antevens/smart-wallplate/docs/renders/eu_5v_board_copper_back.png

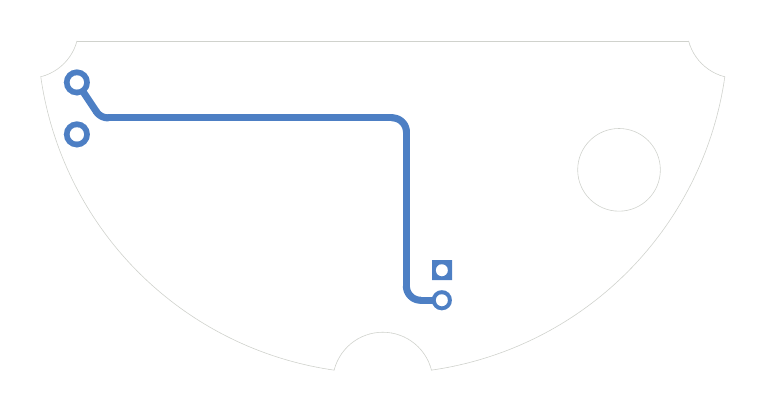
docs/renders/eu_5v_board_copper_back.png
