antevens/smart-wallplate/docs/renders/eu_back.png

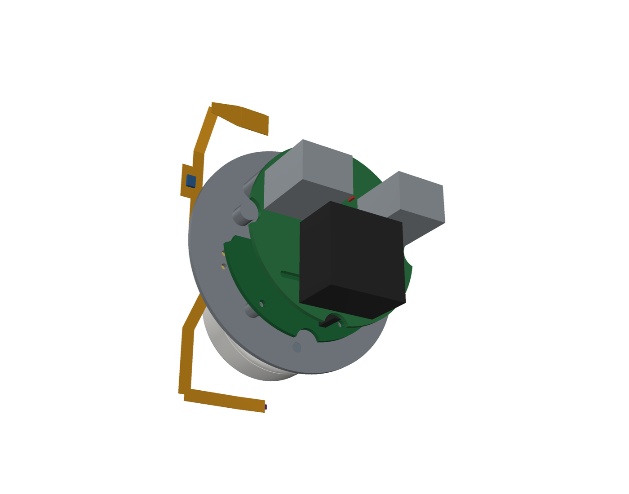
docs/renders/eu_back.png
