antevens/smart-wallplate/docs/renders/power_jumper_copper_back.png

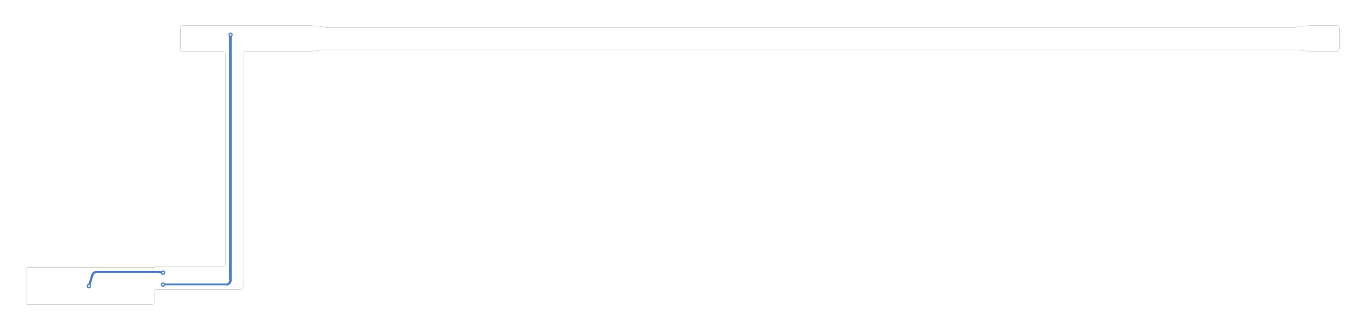
docs/renders/power_jumper_copper_back.png
