antevens/smart-wallplate/reference/v0.1-openscad/renders/01_front.png

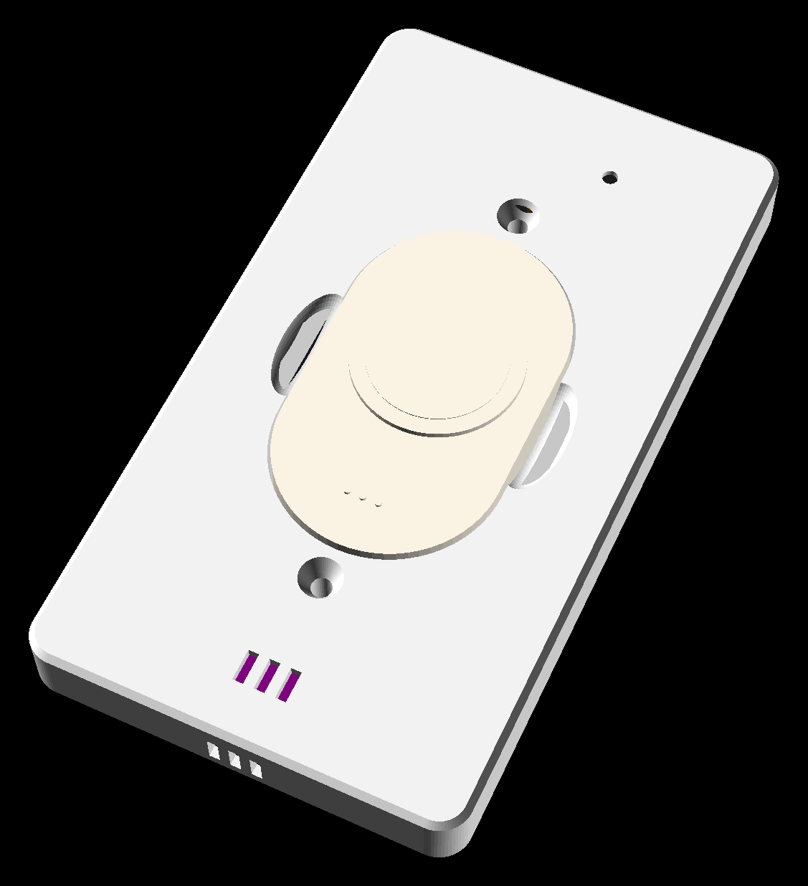
reference/v0.1-openscad/renders/01_front.png
