antevens/smart-wallplate/reference/v0.1-openscad/renders/02_remote_out.png

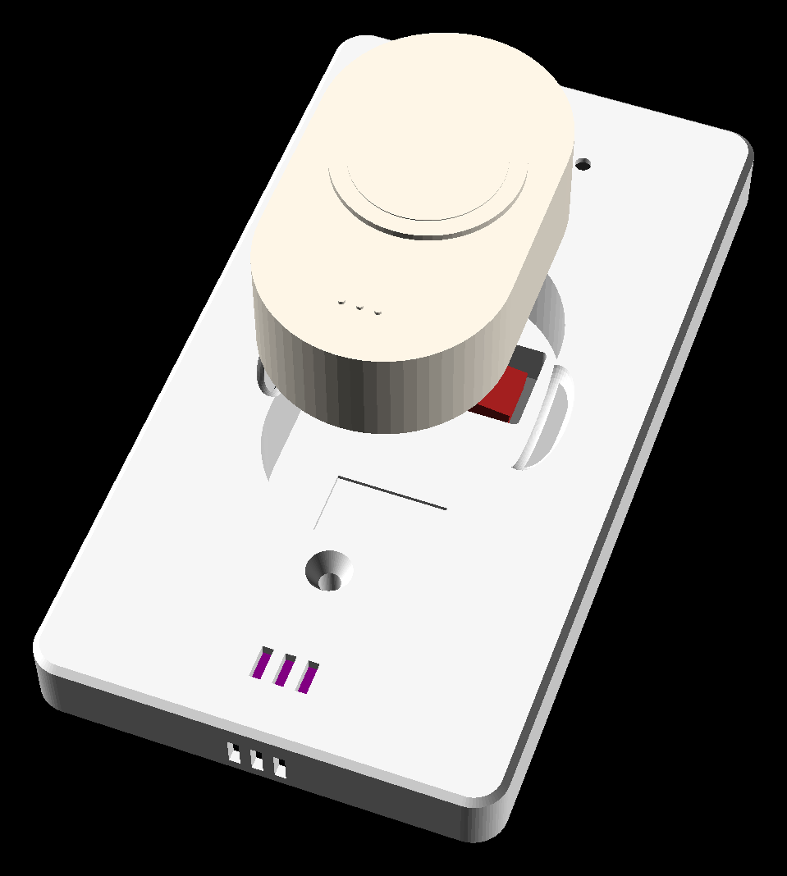
reference/v0.1-openscad/renders/02_remote_out.png
