antevens/smart-wallplate/reference/v0.1-openscad/renders/03_section.png

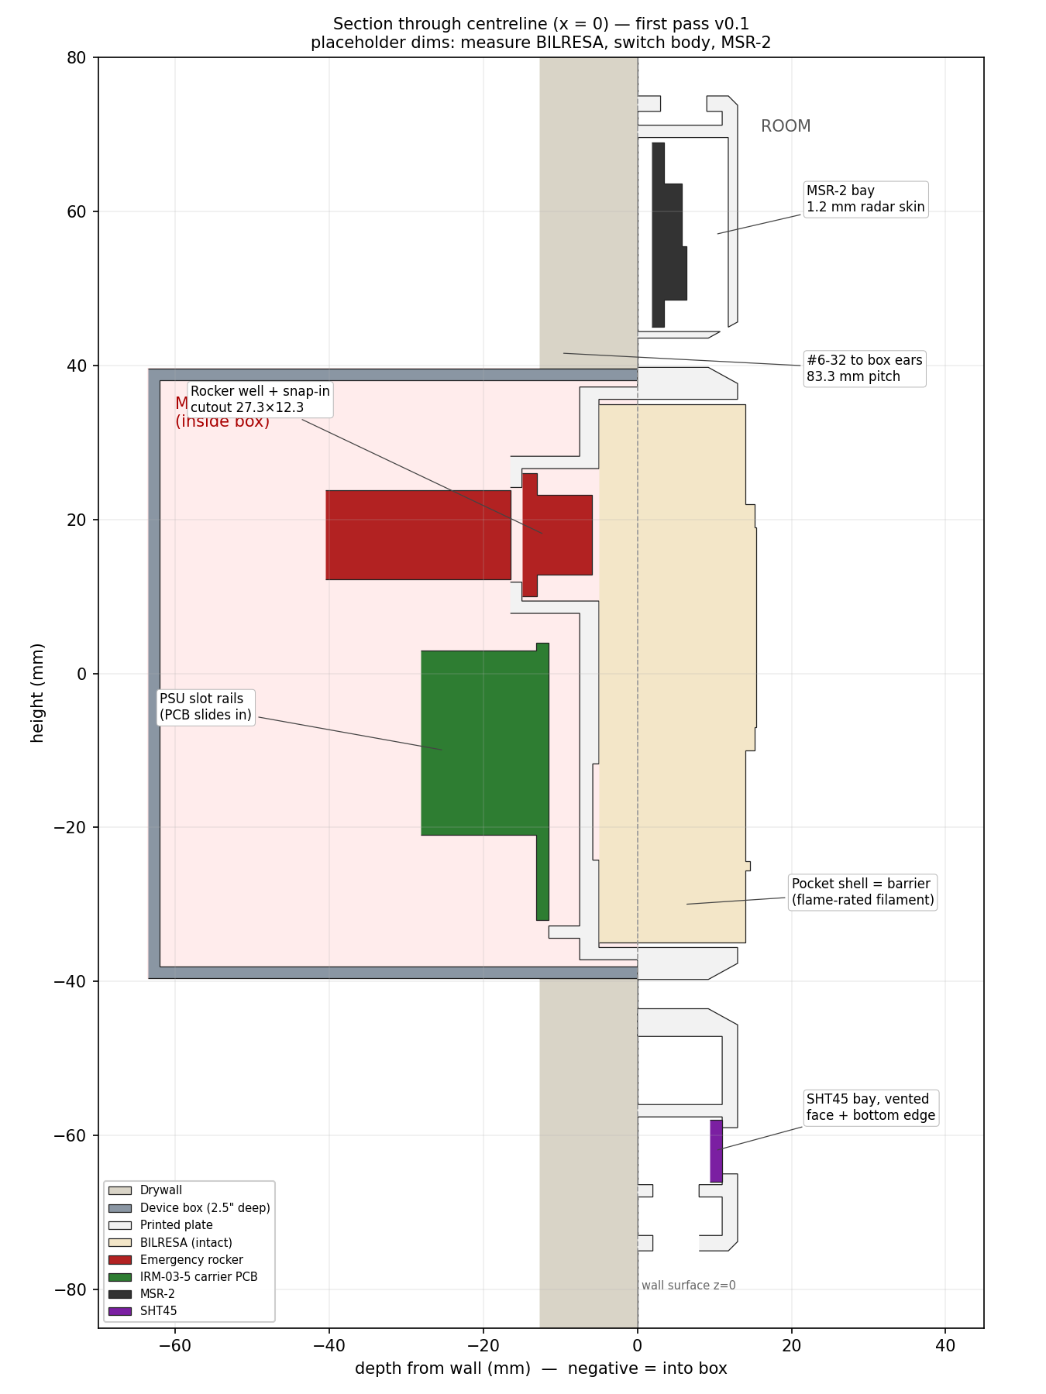
reference/v0.1-openscad/renders/03_section.png
