antevens/smart-wallplate/reference/v0.1-openscad/renders/04_back_mains_side.png

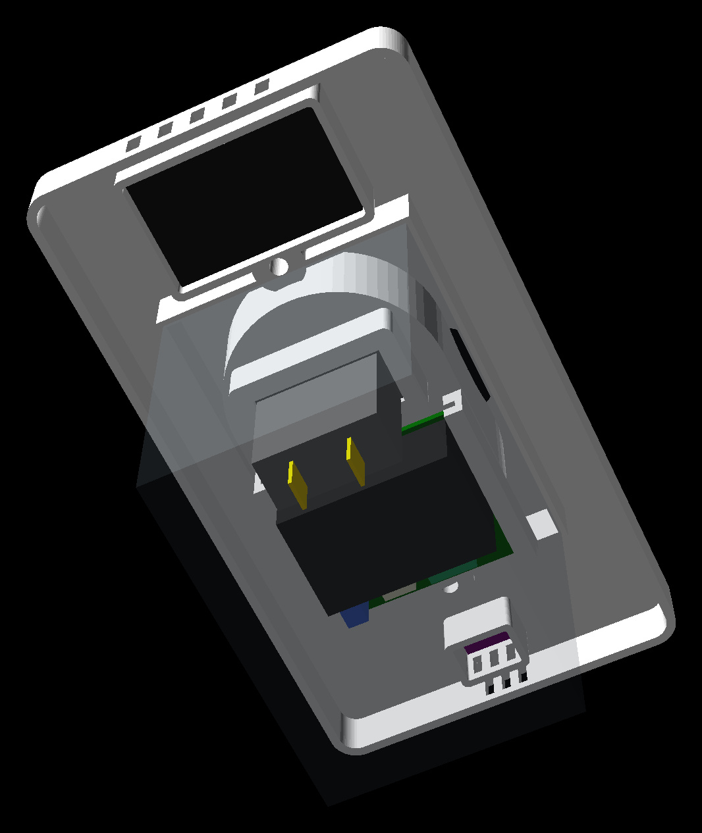
reference/v0.1-openscad/renders/04_back_mains_side.png
