antevens/smart-wallplate/pcb/eu/kicad/3d/WAGO_2604-3102_1x02_P5.00mm_Vertical.step

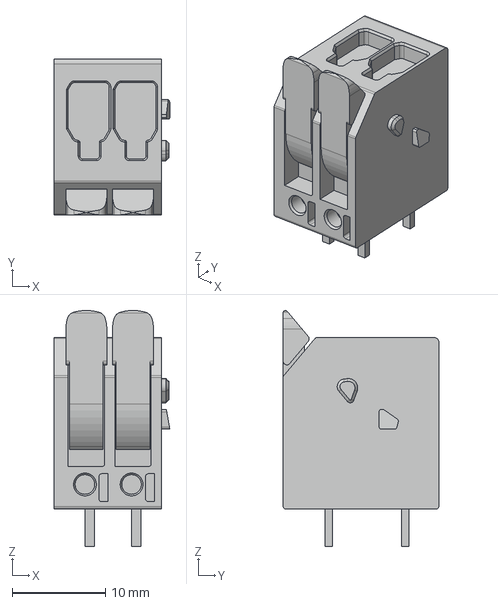
[picture p71: CAD file, 2026-10-09]
pcb/eu/kicad/3d/WAGO_2604-3102_1x02_P5.00mm_Vertical.step
12.4 x 16.7 x 25.3 mm
