antevens/smart-wallplate/print/posts_PC-FR.3mf

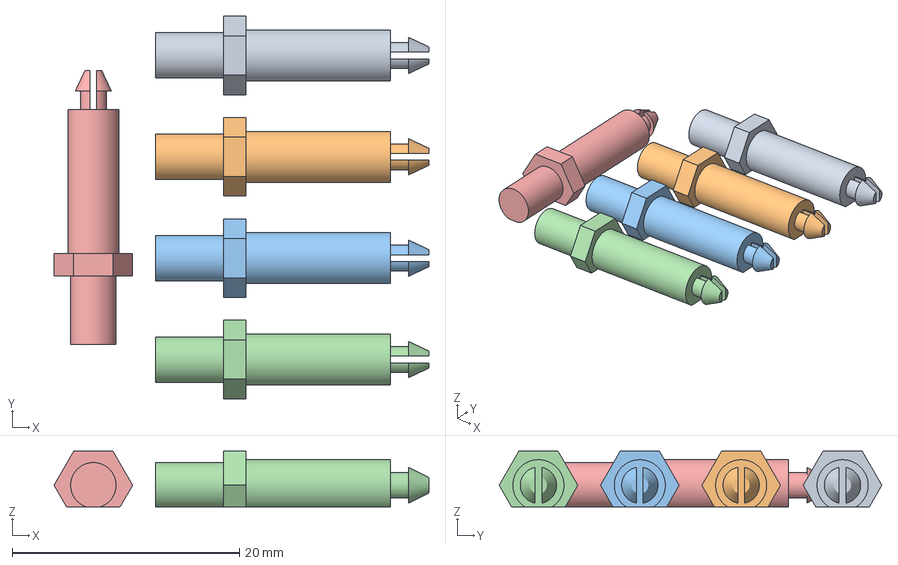
[picture p72: CAD file, 2026-10-09]
print/posts_PC-FR.3mf
33.0 x 33.7 x 4.90 mm
post.stl x 5
