antevens/smart-wallplate/print/coupons_PETG.3mf

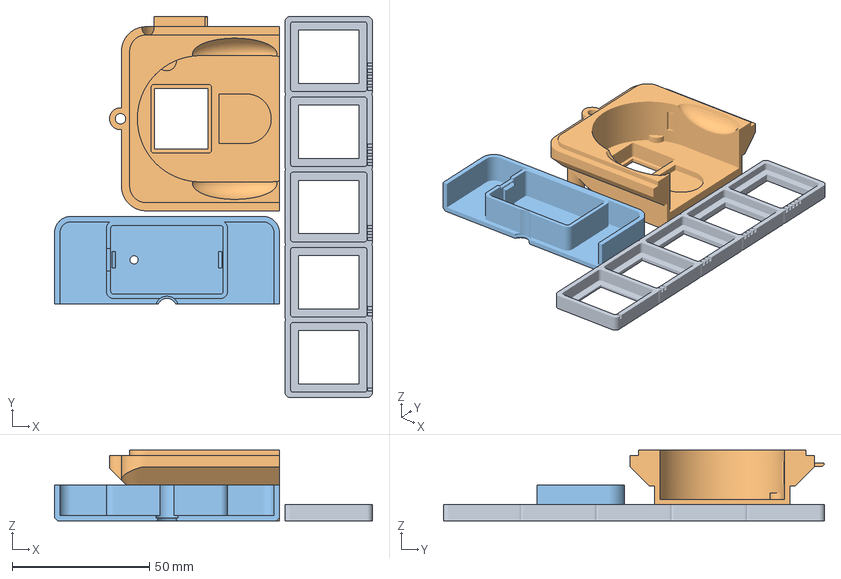
[picture p73: CAD file, 2026-10-09]
print/coupons_PETG.3mf
115.9 x 139.0 x 25.8 mm
coupon_rocker.stl
coupon_pocket_well.stl
coupon_msr.stl
