antevens/smart-wallplate/print/trim_PETG.3mf

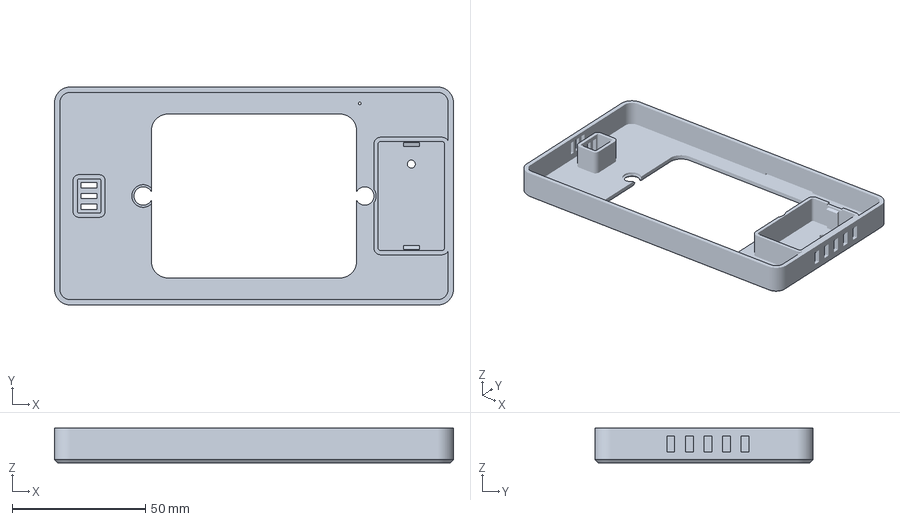
[picture p74: CAD file, 2026-10-09]
print/trim_PETG.3mf
150.0 x 82.0 x 13.0 mm
