antevens/smart-wallplate/print/eu_trim_PETG.3mf

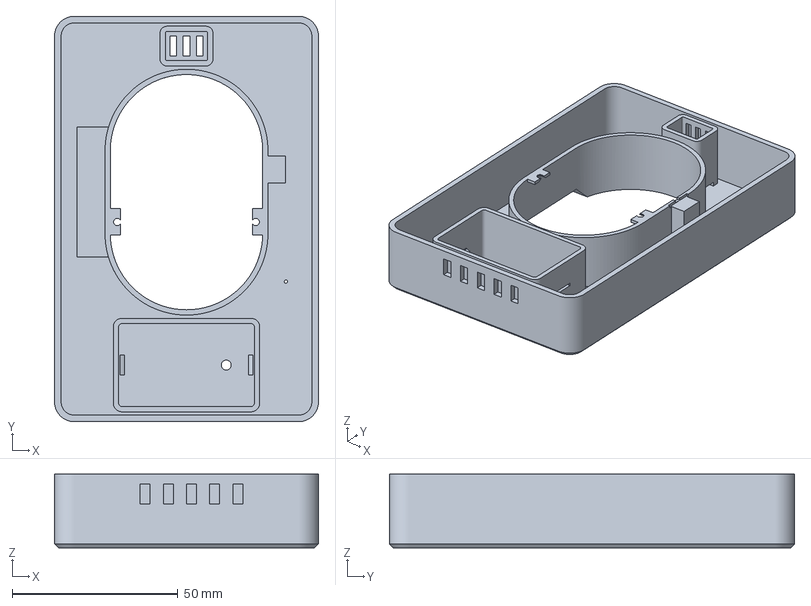
[picture p75: CAD file, 2026-10-09]
print/eu_trim_PETG.3mf
79.7 x 122.4 x 22.2 mm
